Kacman62/CyberWatch32/PCBFiles/CyberWatch32KiCadFilesV1B/STM32 Cyber Watch.kicad_sch

## KiCad design PCBFiles/CyberWatch32KiCadFilesV1B/STM32 Cyber Watch.kicad_sch (2025-10-22)

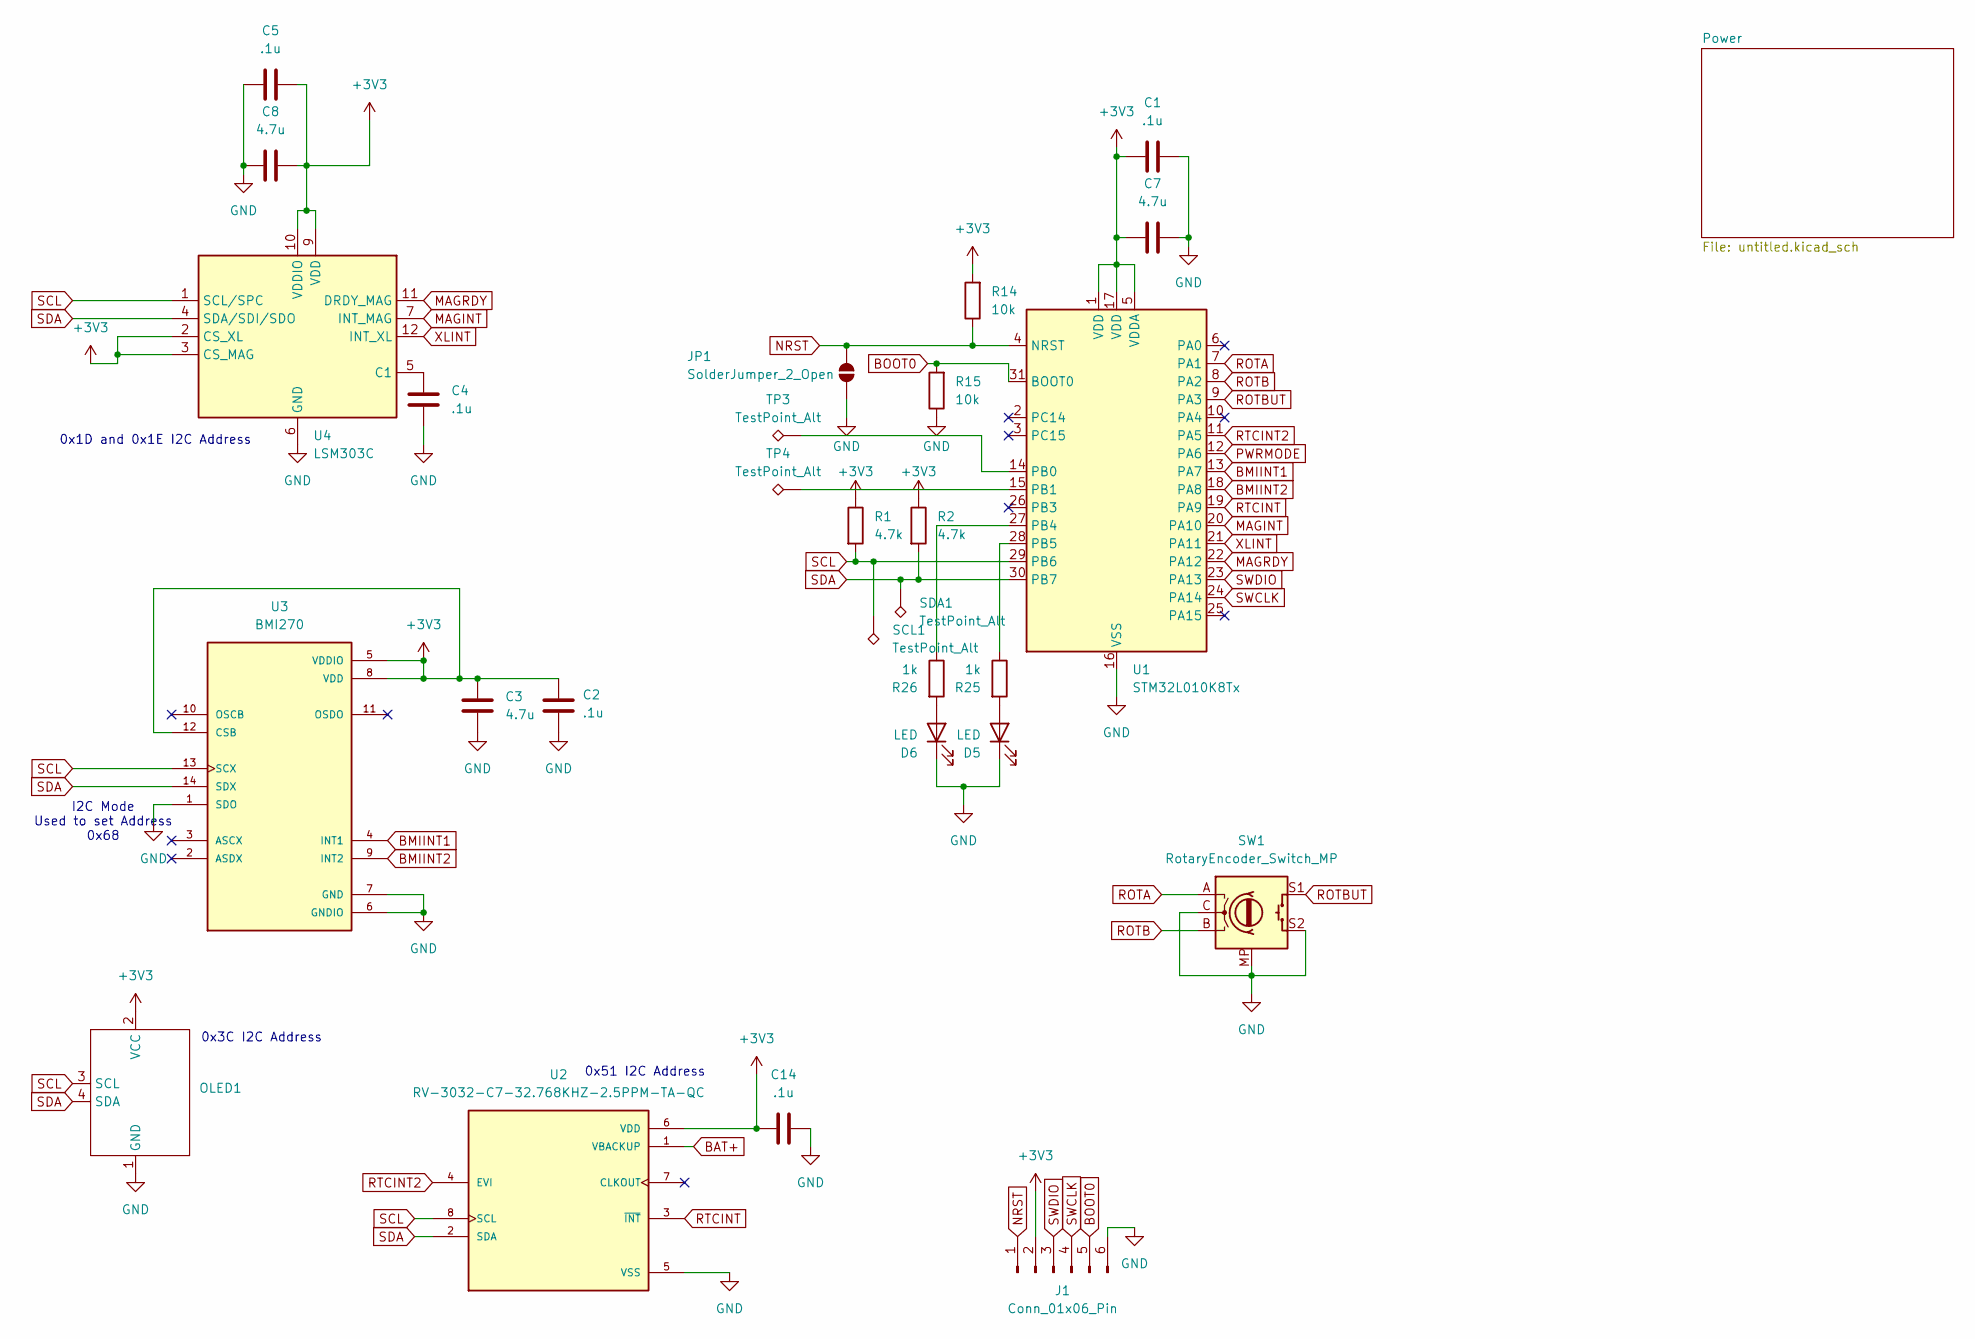
[picture p6: schematic STM32 Cyber Watch.kicad_sch]

Parts:
C1, C2, C4, C5, C14: .1u; C_0603_1608Metric
C3, C7, C8: 4.7u; C_0603_1608Metric
D5, D6: LED; LED_0603_1608Metric
J1: Conn_01x06_Pin; PinHeader_1x06_P2.54mm_Vertical
JP1: SolderJumper_2_Open; SolderJumper-2_P1.3mm_Open_RoundedPad1.0x1.5mm
OLED1: 0.96 OLED I2C
R1, R2: 4.7k; R_0603_1608Metric
R14, R15: 10k; R_0603_1608Metric
R25, R26: 1k; R_0603_1608Metric
SCL1: TestPoint_Alt; TestPoint_Pad_D2.5mm
SDA1: TestPoint_Alt; TestPoint_Pad_D2.5mm
SW1: RotaryEncoder_Switch_MP; RotaryEncoder_Bourns_Horizontal_PEC12R-2x17F-Sxxxx
TP3, TP4: TestPoint_Alt; TestPoint_Pad_D2.5mm
U1: STM32L010K8Tx; LQFP-32_7x7mm_P0.8mm
U2: RV-3032-C7-32.768KHZ-2.5PPM-TA-QC; IC_RV-3032-C7-32.768KHZ-2.5PPM-TA-QC; PARTREV 1.4
U3: BMI270; XDCR_BMI270
U4: LSM303C; LGA-12_2x2mm_P0.5mm

Connections:
+3V3: C1.1, C2.2, C3.2, C5.2, C7.2, C8.1, C14.1, J1.2, OLED1.2 (VCC), R1.1, R2.1, R14.2, U1.1 (VDD), U1.5 (VDDA), U1.17 (VDD), U2.6 (VDD), U3.5 (VDDIO), U3.8 (VDD), U3.12 (CSB), U4.2 (CS_XL), U4.3 (CS_MAG), U4.9 (VDD), U4.10 (VDDIO)
BAT+: U2.1 (VBACKUP)
BMIINT1: U1.13 (PA7), U3.4 (INT1)
BMIINT2: U1.18 (PA8), U3.9 (INT2)
BOOT0: J1.5, R15.2, U1.31 (BOOT0)
GND: C1.2, C2.1, C3.1, C4.1, C5.1, C7.1, C8.2, C14.2, D5.1 (K), D6.1 (K), J1.6, JP1.2 (B), OLED1.1 (GND), R15.1, SW1.C, SW1.MP, SW1.S2, U1.16 (VSS), U1.32 (VSS), U2.5 (VSS), U3.1 (SDO), U3.6 (GNDIO), U3.7 (GND), U4.6 (GND), U4.8 (GND)
MAGINT: U1.20 (PA10), U4.7 (INT_MAG)
MAGRDY: U1.22 (PA12), U4.11 (DRDY_MAG)
NRST: J1.1, JP1.1 (A), R14.1, U1.4 (NRST)
unnamed: C4.2, U4.5 (C1)
unnamed: D5.2 (A), R25.2
unnamed: D6.2 (A), R26.2
unnamed: R25.1, U1.28 (PB5)
unnamed: R26.1, U1.27 (PB4)
unnamed: TP3.1, U1.14 (PB0)
unnamed: TP4.1, U1.15 (PB1)
PWRMODE: U1.12 (PA6)
ROTA: SW1.A, U1.7 (PA1)
ROTB: SW1.B, U1.8 (PA2)
ROTBUT: SW1.S1, U1.9 (PA3)
RTCINT: U1.19 (PA9), U2.3 (~INT)
RTCINT2: U1.11 (PA5), U2.4 (EVI)
SCL: OLED1.3 (SCL), R1.2, SCL1.1, U1.29 (PB6), U2.8 (SCL), U3.13 (SCX), U4.1 (SCL/SPC)
SDA: OLED1.4 (SDA), R2.2, SDA1.1, U1.30 (PB7), U2.2 (SDA), U3.14 (SDX), U4.4 (SDA/SDI/SDO)
SWCLK: J1.4, U1.24 (PA14)
SWDIO: J1.3, U1.23 (PA13)
XLINT: U1.21 (PA11), U4.12 (INT_XL)

Notes on the sheet:
0x51 I2C Address
I2C Mode Used to set Address 0x68
0x1D and 0x1E I2C Address
0x3C I2C Address
