Kacman62/CyberWatch32/PCBFiles/CyberWatch32KiCadFilesV1B/untitled.kicad_sch

## KiCad design PCBFiles/CyberWatch32KiCadFilesV1B/untitled.kicad_sch (2025-10-22)

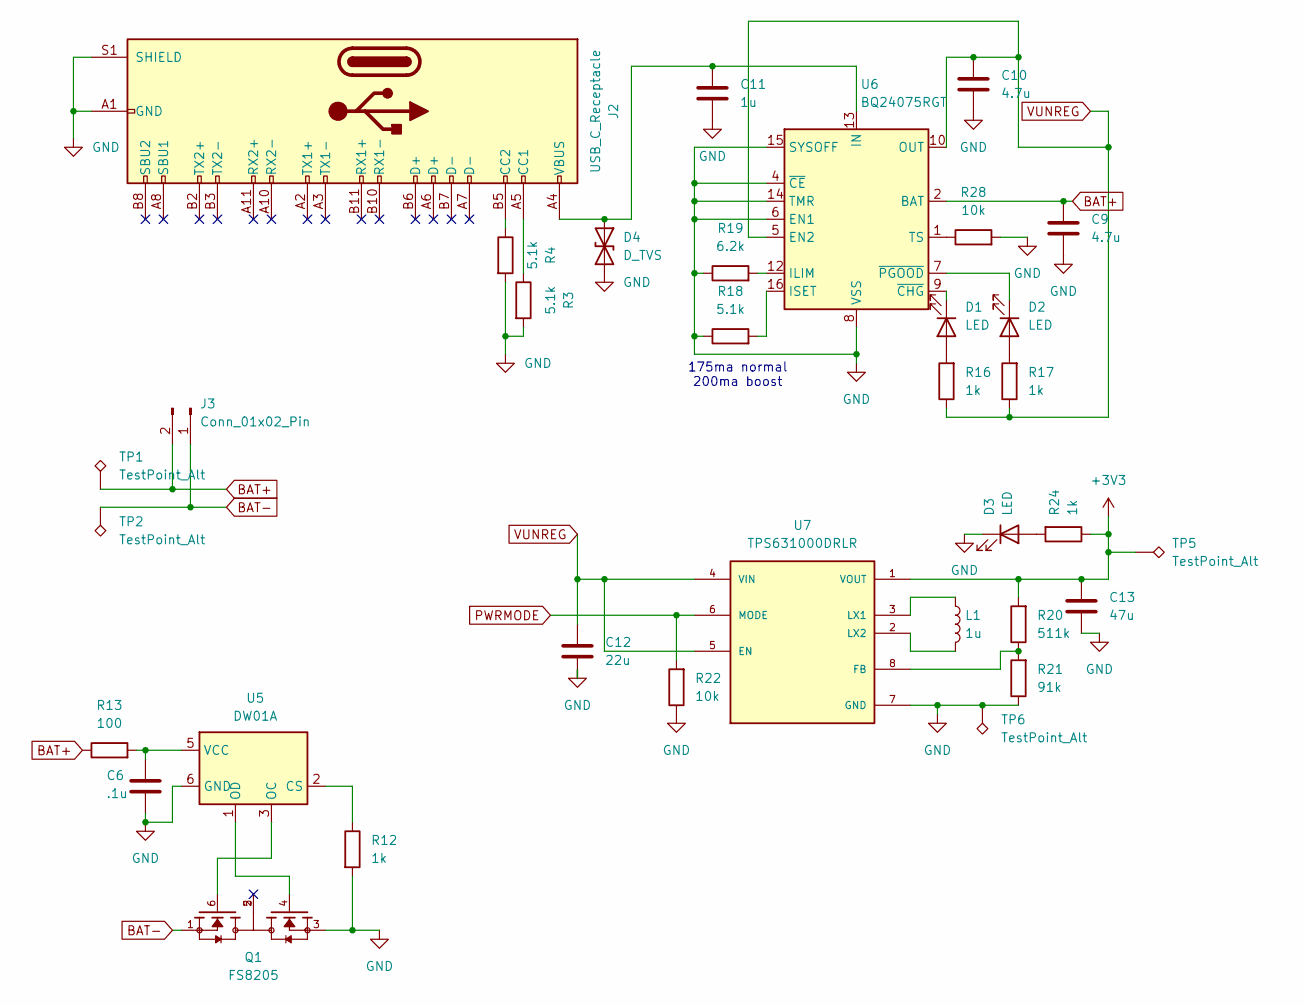
[picture p7: schematic untitled.kicad_sch]

Parts:
C6: .1u; C_0603_1608Metric
C9, C10: 4.7u; C_0603_1608Metric
C11: 1u; C_0603_1608Metric
C12: 22u; C_0603_1608Metric
C13: 47u; C_0603_1608Metric
D1, D2, D3: LED; LED_0603_1608Metric
D4: D_TVS; SMBJ TVS Diode
J2: USB_C_Receptacle; 24P-Recessed-USB-C
J3: Conn_01x02_Pin; JST_EH_B2B-EH-A_1x02_P2.50mm_Vertical
L1: 1u; L_1008_2520Metric
Q1: FS8205; DFN_2PV33R_STM; PARTREV 1.9
R3, R4, R18: 5.1k; R_0603_1608Metric
R12, R16, R17, R24: 1k; R_0603_1608Metric
R13: 100; R_0603_1608Metric
R19: 6.2k; R_0603_1608Metric
R20: 511k; R_0603_1608Metric
R21: 91k; R_0603_1608Metric
R22, R28: 10k; R_0603_1608Metric
TP1, TP2: TestPoint_Alt; TestPoint_Pad_D4.0mm
TP5, TP6: TestPoint_Alt; TestPoint_Pad_D2.5mm
U5: DW01A; SOT-23-6
U6: BQ24075RGT; QFN16
U7: TPS631000DRLR; SOT50P160X60-8N; PARTREV B

Connections:
+3V3: C13.1, R20.2, R24.1, TP5.1, U7.1 (VOUT)
BAT+: C9.1, J3.2, R13.1, TP1.1, U6.2 (BAT), U6.3 (BAT)
BAT-: J3.1, Q1.1, TP2.1
GND: C6.1, C9.2, C10.2, C11.2, C12.2, C13.2, D3.1 (K), D4.2 (A2), J2.A1 (GND), J2.A12 (GND), J2.B1 (GND), J2.B12 (GND), J2.S1 (SHIELD), Q1.3, R3.2, R4.2, R12.2, R18.1, R19.1, R21.1, R22.1, R28.2, TP6.1, U5.6 (GND), U6.4 (~CE), U6.6 (EN1), U6.8 (VSS), U6.14 (TMR), U6.15 (SYSOFF), U6.17 (VSS), U7.7 (GND)
unnamed: C6.2, R13.2, U5.5 (VCC)
unnamed: C11.1, D4.1 (A1), J2.A4 (VBUS), J2.A9 (VBUS), J2.B4 (VBUS), J2.B9 (VBUS), U6.13 (IN)
unnamed: D1.1 (K), U6.9 (~CHG)
unnamed: D1.2 (A), R16.2
unnamed: D2.1 (K), U6.7 (~PGOOD)
unnamed: D2.2 (A), R17.2
unnamed: D3.2 (A), R24.2
unnamed: J2.A5 (CC1), R3.1
unnamed: J2.B5 (CC2), R4.1
unnamed: L1.1, U7.3 (LX1)
unnamed: L1.2, U7.2 (LX2)
unnamed: Q1.2, Q1.5
unnamed: Q1.4, U5.1 (OD)
unnamed: Q1.6, U5.3 (OC)
unnamed: R12.1, U5.2 (CS)
unnamed: R18.2, U6.16 (ISET)
unnamed: R19.2, U6.12 (ILIM)
unnamed: R20.1, R21.2, U7.8 (FB)
unnamed: R28.1, U6.1 (TS)
PWRMODE: R22.2, U7.6 (MODE)
VUNREG: C10.1, C12.1, R16.1, R17.1, U6.5 (EN2), U6.10 (OUT), U6.11 (OUT), U7.4 (VIN), U7.5 (EN)

Notes on the sheet:
175ma normal 200ma boost
